ECE411-Practicum-Group11/ECE411-PracticumProject-G11/411documents/411_Schedule.pdf

411 Schedule | Nov 2, 2022
Gantt Chart | 3
BOM | 11/7/22 | 11/9/22
L0 and L1 Block Diagram | 11/9/22 | 11/10/22
Code Floppy Derp for button input | 11/10/22 | 11/14/22
Design Review | 11/10/22 | 11/14/22
Code Floppy Derp for ... | 11/14/22 | 11/17/22
Final CAD | 11/14/22 | 11/17/22
Assemble / fab board | 11/16/22 | 11/17/22
Test plan | 11/28/22 | 12/1/22
Demo | 12/9/22 | 12/9/22
